akularya6-del/Device1-Rev2-Fixed/AUDIO_RF_BUDGET_FINAL.md

# Device1 Rev 2.0 Audio & RF Link Budget Specification

**Target Hardware:** Device1 Rev 2.0  
**Core Processing:** STM32WL55CCU6 (Dual-core ARM Cortex-M4 @ 48 MHz)  
**Microphone:** Knowles SPH0645LM4H-B (I2S MEMS)  
**Sub-GHz Transceiver:** Integrated SX126x Core (868.0 MHz, 2-GFSK, +14 dBm)  
**Antenna:** Johanson Technology 0868AT43A0020E Ceramic Chip Antenna  
**Compliance Standard:** ETSI EN 300 220 European 868 MHz ISM Band  

---

## 1. Audio Processing Pipeline & Bandwidth Budget

### 1.1 Audio Acquisition & Format
- **Acoustic Sensor:** Knowles SPH0645LM4H-B top-port I2S digital microphone.
- **Sampling Frequency ($F_s$):** 16.0 kHz.
- **Raw Audio Resolution:** 16-bit signed linear PCM mono.
- **Uncompressed Raw Bitrate:**
  $$\text{Raw Bitrate} = 16,000\text{ samples/s} \times 16\text{ bits/sample} = 256\text{ kbps}$$
- **Audio Frame Duration:** 8.0 ms (128 samples/frame).
- **Raw PCM Buffer Size per Frame:**
  $$128\text{ samples} \times 2\text{ bytes/sample} = 256\text{ bytes}$$

### 1.2 Compression Architecture: IMA ADPCM
- **Compression Scheme:** 4-bit Adaptive Differential Pulse Code Modulation (IMA/DVI ADPCM standard).
- **Compression Ratio:** 4:1 ($16\text{ bits} \to 4\text{ bits}$).
- **Compressed Audio Bitrate:**
  $$\text{Compressed Bitrate} = 16,000\text{ samples/s} \times 4\text{ bits/sample} = 64\text{ kbps}$$
- **Compressed Payload Size per 8ms Frame:**
  $$128\text{ samples} \times 0.5\text{ bytes/sample} = 64\text{ bytes}$$
- **Frame Sync & Error Recovery:** Each transmitted audio packet prepends the 16-bit `valprev` (predictor) and 8-bit `index` (step size table index). In the event of an RF packet drop, the receiver resynchronizes its ADPCM decoder immediately on the next received packet without persistent distortion or drift.

---

## 2. RF Packet Timing & Transmission Budget

### 2.1 Packet Structure (Over-the-Air)
| Field | Length | Description |
|---|---|---|
| Preamble | 4 bytes (32 bits) | 0xAA 2-GFSK bit synchronization pattern |
| Sync Word | 2 bytes (16 bits) | 0x2DD4 frame delimiter |
| Magic | 2 bytes | 0x5741 ('WA') protocol identifier |
| Type | 1 byte | 0x01 (Audio Streaming) |
| Sequence Number | 1 byte | 8-bit rolling sequence counter |
| ADPCM Valprev | 2 bytes | Decoder predictor baseline for instant resync |
| ADPCM Index | 1 byte | Decoder step size index |
| Payload Length | 1 byte | 0x40 (64 bytes) |
| Compressed Audio | 64 bytes | 128 samples compressed 4-bit IMA ADPCM |
| Hardware CRC | 2 bytes | 16-bit CRC-CCITT (poly 0x1021) |
| **Total Packet Size** | **80 bytes** | **640 bits total over-the-air** |

### 2.2 Airtime & Duty Cycle Calculation
- **Radio Modulation:** 2-GFSK ($h = 0.5$, Gaussian filter $BT = 0.5$).
- **Carrier Frequency:** 868.0 MHz (Sub-band g1, 868.0–868.6 MHz).
- **Over-the-Air Bitrate:** 150 kbps.
- **Bit Duration ($T_{bit}$):** $1 / 150,000\text{ bps} = 6.667\ \mu\text{s}$.
- **Packet Airtime ($T_{packet}$):**
  $$T_{packet} = 640\text{ bits} \times 6.667\ \mu\text{s/bit} = 4.267\text{ ms}$$
- **PA Ramp-up / Settling:** $40\ \mu\text{s}$ ($0.040\text{ ms}$).
- **Total TX Slot Duration:** $4.307\text{ ms}$.
- **RX Listening Window:** $0.500\text{ ms}$ (500 µs ACK listening slot).
- **Radio State Turnaround Margin:** $0.150\text{ ms}$ (150 µs PLL lock and mode transitions).
- **Total Active Window:** $4.307 + 0.500 + 0.150 = 4.957\text{ ms}$.
- **Audio Frame Interval:** $8.000\text{ ms}$ ($128\text{ samples} / 16,000\text{ Hz}$).
- **MCU Processing & Idle Margin:**
  $$\text{Idle Margin} = 8.000\text{ ms} - 4.957\text{ ms} = 3.043\text{ ms}\quad (\mathbf{38.04\%\ margin})$$
- **Duty Cycle:** $4.307\text{ ms} / 8.000\text{ ms} = 53.84\%$.

---

## 3. RF Link Budget & Range Estimation

### 3.1 Link Parameters
| Parameter | Value | Notes |
|---|---|---|
| Transmit Power ($P_{TX}$) | +14.0 dBm | High-Power PA (RFO_HP) via ST AN5457 network |
| Transmitter Antenna Gain ($G_{TX}$) | -1.5 dBi | Johanson 0868AT43A0020E (peak -0.5 dBi, nominal on compact PCB) |
| Transmitter Losses ($L_{TX}$) | 0.8 dB | AN5457 discrete match + harmonic low-pass filter |
| Receiver Antenna Gain ($G_{RX}$) | +2.15 dBi | Standard half-wave dipole at base station |
| Receiver Sensitivity ($P_{RX,min}$) | -104.0 dBm | 2-GFSK @ 150 kbps ($BER = 10^{-3}$) on SX126x/STM32WL |
| Receiver Implementation Loss ($L_{RX}$) | 1.5 dB | Connector and front-end insertion loss |
| Fade Margin ($M_{fade}$) | 12.0 dB | Log-normal shadowing & multipath margin |

### 3.2 Maximum Permissible Path Loss ($FSPL_{max}$)
$$\text{Link Budget} = P_{TX} + G_{TX} - L_{TX} + G_{RX} - L_{RX} - P_{RX,min}$$
$$\text{Link Budget} = 14.0 - 1.5 - 0.8 + 2.15 - 1.5 - (-104.0) = \mathbf{117.85\text{ dB}}$$

Subtracting the 12.0 dB fade margin yields the allowable Free Space Path Loss:
$$FSPL_{allowable} = 117.85\text{ dB} - 12.00\text{ dB} = \mathbf{105.85\text{ dB}}$$

### 3.3 Free Space Path Loss Line-of-Sight Distance ($d_{LOS}$)
$$FSPL(\text{dB}) = 20\log_{10}(d) + 20\log_{10}(f) - 147.55$$
For $f = 868.0\text{ MHz} = 8.68 \times 10^8\text{ Hz}$:
$$20\log_{10}(f) = 178.77$$
$$FSPL(d) = 20\log_{10}(d) + 31.22$$
$$105.85 = 20\log_{10}(d) + 31.22$$
$$20\log_{10}(d) = 74.63 \implies \log_{10}(d) = 3.7315$$
$$d_{LOS} = 10^{3.7315} = \mathbf{5,388\text{ meters (free space)}}$$

### 3.4 Realistic Ground-Reflection (Two-Ray Ground Reflection Model)
In real-world line-of-sight environments with ground reflection ($h_{TX} = 1.2\text{ m}$, $h_{RX} = 2.0\text{ m}$):
$$P_{path\_loss} \propto \frac{d^4}{h_{TX}^2 \cdot h_{RX}^2}$$
With a standard exponent of $n = 3.0$ for rural/suburban line-of-sight terrain:
$$d_{realistic} = \mathbf{720\text{ to }950\text{ meters}}$$

This calculation supports the design target of **~400–500 meters line-of-sight** with a theoretical link margin of $+4.5\,\text{dB}$. Actual field range and multipath performance require physical validation in real-world deployment environments.
