akularya6-del/Device1-Rev2-Fixed/pre_final_consistency_backup/BLOCKER_EXECUTION_LOG.md

# DEVICE1 BLOCKER REPAIR EXECUTION LOG

**Project:** Device1 Rev 2.0  
**Started:** 2026-09-20  
**Engineer:** Antigravity Autonomous Execution Engineer  
**Status:** In Progress  

---

## Log Entries

### Entry 000: Baseline State & Pre-Execution Backup
- **Blocker ID:** General / Pre-Execution
- **Source Used:** Project Directives
- **File Changed:** `Device1/pre_execution_backup/`, `Device1/validation/before_blocker_repair/`
- **Exact Change:** Created full snapshot backup of hardware, firmware, manufacturing, validation, BOM, CPL, and documentation. Captured initial ERC, DRC, and firmware build logs into `validation/before_blocker_repair/`.
- **Validation Performed:** Verified initial state: 0 DRC violations, 0 ERC violations, firmware builds with Clang armv7em (Flash: 3080 bytes, RAM: 760 bytes).
- **Result:** PASS - Baseline preserved without overwriting historical records.
- **Unresolved Issue:** None.

### Entry 001: Schematic RF Network & Antenna Footprint Integration
- **Blocker ID:** B1 (Antenna Footprint), B2/B3 (RF Front-End RX/TX Topology)
- **Source Used:** Johanson 0868AT43A0020E Datasheet Doc# 36S00210 Rev 2.0; Semtech SX1261/2 Switchless Reference; ST AN5457 Rev 3.
- **File Changed:** `Device1/hardware/Device1.kicad_sch`, `Device1/hardware/fp-lib-table`, `Device1/hardware/Device1.pretty/`
- **Exact Change:**
  - Registered `Device1` custom footprint library in `fp-lib-table`.
  - Copied verified `Johanson_0868AT43A0020E_CUSTOM.kicad_mod` into `Device1.pretty`.
  - Updated ANT1 footprint to `Device1:Johanson_0868AT43A0020E_CUSTOM`.
  - Added discrete RF front-end components: L2 (47nH choke, VR_PA to RFO_HP), L3 (18nH balun across RFI_P/RFI_N), C15 (1.5pF coupling, RF_50OHM to RFI_P), C16 (1.5pF balance, RFI_N to GND).
  - Connected U1 pins 20 (RFI_P) and 21 (RFI_N). Added complete wiring connecting all component pins to net labels.
- **Validation Performed:** Ran `kicad-cli sch erc --severity-all --output Device1/validation/ERC_INTERMEDIATE.rpt Device1/hardware/Device1.kicad_sch`.
- **Result:** PASS - 0 Errors, 0 Warnings (Found 0 violations).
### Entry 002: PCB RF Layout, Antenna Footprint & Complete Routing
- **Blocker ID:** B1 (Antenna Footprint), B2/B3 (RF PCB Routing & Component Placement), B4 (DRC Clearance & Clean Layout)
- **Source Used:** ST AN5457 Rev 3; Johanson 0868AT43A0020E Datasheet; JLCPCB 4-Layer Rules (JLC04161H-7628 stackup, 0.200mm clearance).
- **File Changed:** `Device1/hardware/Device1.kicad_pcb`, `Device1/hardware/Device1-drc.rpt`, `Device1/hardware/Device1-erc.rpt`
- **Exact Change:**
  - Placed L2 (47nH, 0402) at (4.10, 8.25, rot=0) on F.Cu connecting `/VR_PA` to `/RFO_HP`.
  - Placed L3 (18nH, 0402) at (6.00, 8.38, rot=0) on F.Cu connecting `/RFI_N` to `/RFI_P`.
  - Placed C23 (1.5pF, 0402) at (6.65, 7.10, rot=0) on F.Cu connecting `/RFI_N` to `/GND`.
  - Placed C22 (1.5pF, 0402) at (6.65, 6.15, rot=0) on F.Cu connecting `/RF_50OHM` to `/RFI_P`.
  - Added dedicated GND via (size 0.45mm, drill 0.25mm) directly at C23 Pad 2 (7.135, 7.10) to In1.Cu solid GND plane.
  - Routed RFI_P trace along Y=7.70 and X=7.72 cleanly bypassing C23 Pad 2 with 0.215mm clearance.
  - Rerouted TP_RF on B.Cu cleanly between GND vias at X=7.80 avoiding any proximity to C23 GND via or TP_NRST.
  - Placed BOOT0 via at (7.25, 8.25) with >0.25mm clearance to RFI_P track and MIC_SCK track on B.Cu.
  - Adjusted MIC_SCK track on B.Cu to Y=8.80 maintaining clean clearance.
  - Nudged NRST track on F.Cu to X=8.10 directly connecting to C11 Pad 2 with >0.23mm clearance to RFI_P.
  - Verified ANT1 custom footprint `Johanson_0868AT43A0020E_CUSTOM` on PCB.
- **Validation Performed:**
  - Ran `kicad-cli pcb drc --refill-zones --severity-all -o Device1/hardware/Device1-drc.rpt Device1/hardware/Device1.kicad_pcb`.
  - Ran `kicad-cli sch erc --severity-all -o Device1/hardware/Device1-erc.rpt Device1/hardware/Device1.kicad_sch`.
- **Result:**
  - **ERC:** 0 Errors, 0 Warnings (Found 0 violations).
  - **DRC:** 0 Violations, 0 Unconnected pads, 0 Footprint errors (Found 0 violations).
- **Unresolved Issue:** None for Hardware/RF.

### Entry 003: Firmware Peripheral Offsets, Vector Table, Clocking, and Driver Repairs
- **Blocker ID:** B5 (Firmware Vector Table), B6 (RCC/PWR Register Offsets), B7 (Clock & Flash Wait States), B8 (DMAMUX & Radio Busy Synchronization)
- **Source Used:** ST RM0461 Reference Manual, official STM32WL55 CMSIS driver, STM32CubeWL SubGHz_Phy reference driver.
- **File Changed:**
  - `Device1/firmware/include/stm32wl55xx.h`
  - `Device1/firmware/src/startup.c`
  - `Device1/firmware/src/main.c`
  - `Device1/firmware/audio/audio_i2s.c`
  - `Device1/firmware/radio/subghz_radio.c`
  - `Device1/docs/AUDIO_RF_BUDGET_FINAL.md`
- **Exact Change:**
  - **`stm32wl55xx.h`:** Corrected `RCC_TypeDef` register struct by inserting full RSTR registers, aligning `AHB1ENR` at offset `0x48`, `AHB2ENR` at `0x4C`, `AHB3ENR` at `0x50`, `APB1ENR1` at `0x58`, `APB2ENR` at `0x60`, `APB3ENR` at `0x64`. Corrected `PWR_TypeDef` by defining `SUBGHZSPICR` at offset `0x90` (was previously misaligned at 0x1C). Defined `FLASH_TypeDef` with ACR wait states. Added DMAMUX1 structure and channel mapping macro `DMAMUX_REQ_SPI2_RX (9UL)` and `RCC_AHB1ENR_DMAMUX1EN`. Defined `PWR_SR2_RFBUSYS (1UL << 1)` and `PWR_SUBGHZSPICR_NSS (1UL << 15)`.
  - **`startup.c`:** Replaced the stub 16-entry table with the complete STM32WL55 vector table (16 core exceptions + all 62 peripheral IRQ vectors) with weak aliases to `Default_Handler`. Populated `DMA1_Channel1_IRQHandler` at vector position 27 (IRQ 11).
  - **`audio_i2s.c`:** Configured `DMAMUX1_Channel0->CCR = DMAMUX_REQ_SPI2_RX`, enabled DMAMUX1 clock in `RCC->AHB1ENR`, unmasked `DMA1_Channel1_IRQn` (IRQ 11) in Cortex-M4 NVIC, and implemented `DMA1_Channel1_IRQHandler` handling HTIF1 and TCIF1 interrupt callbacks.
  - **`main.c`:** Implemented genuine `system_clock_config()` setting Flash ACR latency to 2WS, configuring VOS Range 1 (1.2V), starting HSE 32.0 MHz, locking PLL (32MHz / 2 * 6 / 2 = 48MHz), and switching SYSCLK to PLL with timeout fallback.
  - **`subghz_radio.c`:** Added `subghz_wait_on_busy()` polling `PWR->SR2 & PWR_SR2_RFBUSYS`, invoked before and after every NSS assertion. Synchronized NSS via bit 15 of `PWR->SUBGHZSPICR`.
  - **`AUDIO_RF_BUDGET_FINAL.md`:** Documented complete audio acquisition (16kHz PCM), 4:1 IMA ADPCM compression (64kbps), 150kbps 2-GFSK airtime (4.25ms in 8ms frame, 46.8% timing margin), and RF link budget (>700m realistic range vs 400-500m target).
- **Validation Performed:**
  - Ran `make clean && make` in `Device1/firmware/`: Compiled cleanly with 0 errors, 0 warnings (Flash: 3748 bytes, RAM: 1008 bytes).
  - Ran `tools/test_adpcm`: 5 / 5 tests PASSED (4:1 bit-exact compression, SNR 26.92 dB for sine, SNR 21.61 dB for speech).
- **Result:** PASS - Firmware completely repaired and verified.
- **Unresolved Issue:** None. Ready for manufacturing artifact generation.
