akularya6-del/Device1-Rev2-Fixed/pre_final_consistency_backup/hardware/test_step7_solved_drc.txt

** Drc report for test_step7_solved.kicad_pcb **
** Created on 2026-09-20T17:00:53 **
** Report includes: Errors, Warnings, Exclusions **

** Found 24 DRC violations **
[clearance]: Clearance violation ( clearance 0.2000 mm; actual 0.1000 mm)
    Local override; error
    @(6.6000 mm, 26.2000 mm): Via [/MIC_WS] on F.Cu - B.Cu
    @(1.8630 mm, 25.8000 mm): Track [/GATE_OC] on F.Cu, length 5.6370 mm
[shorting_items]: Items shorting two nets (nets /MIC_WS and /MIC_SD)
    Local override; error
    @(6.6000 mm, 26.2000 mm): Via [/MIC_WS] on F.Cu - B.Cu
    @(0.7500 mm, 26.0000 mm): Track [/MIC_SD] on B.Cu, length 6.7500 mm
[clearance]: Clearance violation ( clearance 0.2000 mm; actual 0.1500 mm)
    Local override; error
    @(0.4500 mm, 13.3000 mm): Track [/MIC_WS] on B.Cu, length 12.9000 mm
    @(3.2000 mm, 15.0000 mm): Track [/MIC_SD] on B.Cu, length 2.4500 mm
[clearance]: Clearance violation ( clearance 0.2000 mm; actual 0.0500 mm)
    Local override; error
    @(0.4500 mm, 26.2000 mm): Track [/MIC_WS] on B.Cu, length 6.1500 mm
    @(0.7500 mm, 26.0000 mm): Track [/MIC_SD] on B.Cu, length 6.7500 mm
[clearance]: Clearance violation ( clearance 0.2000 mm; actual 0.1750 mm)
    Local override; error
    @(2.2000 mm, 15.7500 mm): Pad 1 [/SWDIO] of TP_SWDIO on B.Cu
    @(3.2000 mm, 15.0000 mm): Track [/MIC_SD] on B.Cu, length 2.4500 mm
[clearance]: Clearance violation ( clearance 0.2000 mm; actual 0.0500 mm)
    Local override; error
    @(12.1500 mm, 12.0000 mm): Track [/LED_R_DRV] on B.Cu, length 6.0000 mm
    @(11.8000 mm, 12.7500 mm): Via [/CHG_STAT] on F.Cu - B.Cu
[clearance]: Clearance violation ( clearance 0.2000 mm; actual 0.1000 mm)
    Local override; error
    @(7.5000 mm, 25.8000 mm): Track [/GATE_OC] on F.Cu, length 1.6000 mm
    @(7.5000 mm, 26.2000 mm): Via [/MIC_SD] on F.Cu - B.Cu
[tracks_crossing]: Tracks crossing
    Local override; error
    @(11.8000 mm, 17.8000 mm): Track [/CHG_STAT] on B.Cu, length 1.9698 mm
    @(11.4000 mm, 16.5000 mm): Track [/LED_B_DRV] on B.Cu, length 1.5000 mm
[shorting_items]: Items shorting two nets (nets /CHG_STAT and /LED_B_DRV)
    Local override; error
    @(11.8000 mm, 17.8000 mm): Track [/CHG_STAT] on B.Cu, length 1.9698 mm
    @(11.4000 mm, 18.0000 mm): Track [/LED_B_DRV] on B.Cu, length 10.0000 mm
[clearance]: Clearance violation ( clearance 0.2000 mm; actual 0.1000 mm)
    Local override; error
    @(11.8000 mm, 12.7500 mm): Via [/CHG_STAT] on F.Cu - B.Cu
    @(11.4000 mm, 8.8000 mm): Track [/LED_B_DRV] on B.Cu, length 7.7000 mm
[clearance]: Clearance violation ( clearance 0.2000 mm; actual 0.1000 mm)
    Local override; error
    @(1.8630 mm, 25.8000 mm): Track [/GATE_OC] on F.Cu, length 5.6370 mm
    @(7.5000 mm, 26.2000 mm): Via [/MIC_SD] on F.Cu - B.Cu
[shorting_items]: Items shorting two nets (nets /MIC_SCK and /3V3)
    Local override; error
    @(8.4000 mm, 27.2000 mm): Via [/MIC_SCK] on F.Cu - B.Cu
    @(8.4000 mm, 27.1360 mm): Track [/3V3] on F.Cu, length 0.9630 mm
[clearance]: Clearance violation ( clearance 0.2000 mm; actual 0.1750 mm)
    Local override; error
    @(12.7200 mm, 10.7500 mm): Track [/3V3] on F.Cu, length 1.7825 mm
    @(12.2000 mm, 10.2500 mm): Via [/LED_R_DRV] on F.Cu - B.Cu
[shorting_items]: Items shorting two nets (nets /3V3 and /MIC_SCK)
    Local override; error
    @(8.5000 mm, 17.4000 mm): Via [/3V3] on F.Cu - B.Cu
    @(9.2000 mm, 16.5000 mm): Track [/MIC_SCK] on In2.Cu, length 1.4142 mm
[shorting_items]: Items shorting two nets (nets /MIC_SCK and /NRST)
    Local override; error
    @(8.2500 mm, 8.8000 mm): Via [/MIC_SCK] on F.Cu - B.Cu
    @(7.7500 mm, 8.6000 mm): Track [/NRST] on F.Cu, length 0.7500 mm
[shorting_items]: Items shorting two nets (nets /MIC_SCK and /3V3)
    Local override; error
    @(8.4000 mm, 27.2000 mm): Via [/MIC_SCK] on F.Cu - B.Cu
    @(8.4000 mm, 27.1360 mm): Pad 5 [/3V3] of MK1 on F.Cu
[clearance]: Clearance violation ( clearance 0.2000 mm; actual 0.1950 mm)
    Local override; error
    @(12.7200 mm, 9.5000 mm): Track [/3V3] on F.Cu, length 1.2500 mm
    @(12.2000 mm, 10.2500 mm): Via [/LED_R_DRV] on F.Cu - B.Cu
[clearance]: Clearance violation ( clearance 0.2000 mm; actual 0.0162 mm)
    Local override; error
    @(8.2000 mm, 17.5000 mm): Track [/MIC_SCK] on In2.Cu, length 9.0000 mm
    @(8.5000 mm, 17.4000 mm): Via [/3V3] on F.Cu - B.Cu
[shorting_items]: Items shorting two nets (nets /MIC_SCK and /3V3)
    Local override; error
    @(8.4000 mm, 27.2000 mm): Track [/MIC_SCK] on F.Cu, length 0.7580 mm
    @(8.4000 mm, 27.1360 mm): Track [/3V3] on F.Cu, length 0.9630 mm
[clearance]: Clearance violation ( clearance 0.2000 mm; actual 0.0500 mm)
    Local override; error
    @(7.7500 mm, 8.6000 mm): Track [/NRST] on F.Cu, length 0.7500 mm
    @(8.2500 mm, 9.5620 mm): Track [/MIC_SCK] on F.Cu, length 0.7620 mm
[clearance]: Clearance violation ( clearance 0.2000 mm; actual 0.1500 mm)
    Local override; error
    @(0.7500 mm, 15.0000 mm): Track [/MIC_SD] on B.Cu, length 11.0000 mm
    @(1.2000 mm, 24.2000 mm): Via [/GND] on F.Cu - B.Cu
[hole_clearance]: Hole clearance violation (board setup constraints hole clearance 0.2000 mm; actual 0.0000 mm)
    Rule: board setup constraints hole; error
    @(8.4000 mm, 27.1360 mm): Pad 5 [/3V3] of MK1 on F.Cu
    @(8.4000 mm, 27.2000 mm): Via [/MIC_SCK] on F.Cu - B.Cu
[solder_mask_bridge]: Front solder mask aperture bridges items with different nets
    Rule: board setup solder mask min width; error
    @(8.4000 mm, 27.2000 mm): Track [/MIC_SCK] on F.Cu, length 0.7580 mm
    @(8.4000 mm, 27.1360 mm): Pad 5 [/3V3] of MK1 on F.Cu
[solder_mask_bridge]: Front solder mask aperture bridges items with different nets
    Rule: board setup solder mask min width; error
    @(8.4000 mm, 27.2000 mm): Via [/MIC_SCK] on F.Cu - B.Cu
    @(8.4000 mm, 27.1360 mm): Pad 5 [/3V3] of MK1 on F.Cu

** Found 1 unconnected pads **
[unconnected_items]: Missing connection between items
    Local override; error
    @(6.7500 mm, 16.4375 mm): Track [/3V3] on F.Cu, length 0.9625 mm
    @(8.2500 mm, 16.4375 mm): Track [/3V3] on F.Cu, length 0.4125 mm

** Found 0 Footprint errors **

** Ignored checks **
    - Footprint has no courtyard defined
    - Track endpoint not centered on via
    - Tuning profile track geometries
    - Footprint doesn't match symbol's footprint filters
    - Footprint component type doesn't match footprint pads

** End of Report **
