akularya6-del/Device1-Rev2-Fixed/validation/FOOTPRINT_VERIFICATION.md

# Footprint & Physical Package Verification Audit
## Device 1 — Compact Wireless Audio Terminal
**Date:** September 20, 2026  
**Status:** 100% Verified & Validated for JLCPCB 4-Layer SMT Assembly  
**Architecture:** Open Architecture — Strictly Non-TI Components  

---

### 1. Overview & Verification Scope
Every component footprint in the Device 1 CAD design has been verified against manufacturer mechanical specifications, IPC-7351B standards, and JLCPCB manufacturing capabilities. The board features **34 SMD components** arranged with zero courtyard collisions, full thermal reliefs, and precise acoustic port alignment.

---

### 2. Detailed Component Audit Table

| RefDes | Component Description | Manufacturer & Part Number | Package / Footprint | Pad Count & Pitch | Acoustic / Thermal Features | Verification Status |
| :--- | :--- | :--- | :--- | :--- | :--- | :--- |
| **U1** | Dual-Core Sub-GHz Wireless MCU | STMicroelectronics `STM32WL55CCU6` | UFQFPN-48 (7.0 × 7.0 mm, 0.55 mm max height) | 48 pads, 0.50 mm pitch | 5.6 × 5.6 mm Exposed Pad (EP) with 3×3 0.3mm thermal via grid | **VERIFIED** — Solder mask expanded 0.05mm, thermal vias tied to Layer 2 GND |
| **MK1** | Digital I2S Bottom-Port MEMS Mic | Knowles `SPH0645LM4H-B` | Custom LGA-6 (3.50 × 2.65 × 0.98 mm) | 6 perimeter pads, 0.80 mm pitch | 0.50 mm NPTH acoustic through-hole natively embedded in footprint | **VERIFIED** — Solder mask opening rings acoustic port, keepout enforced |
| **ANT1** | 868MHz Ceramic Chip Antenna | Johanson Technology `0868AT43A0020E` | Surface Mount 4-pin (7.0 × 2.0 × 1.2 mm) | 2 functional pads, 2 mechanical end pads | 50-ohm coplanar feed at Pin 1, full copper keepout (Y: 0.0 to 4.2 mm) | **VERIFIED** — Keepout cleared on all 4 copper layers |
| **Y1** | 32.000 MHz HSE Crystal | Murata `XRCGB32M000F1H00R0` | SMD 2016-4P (2.0 × 1.6 × 0.7 mm) | 4 pads (P1/P3 crystal, P2/P4 GND) | Ultra-compact low parasitic layout directly adjacent to U1 OSC pins | **VERIFIED** — Internal STM32WL load cap trimming configured |
| **U5** | 600mA Low-Dropout Regulator | Diodes Inc `AP2112K-3.3TRG1` | SOT-23-5 (2.9 × 1.6 × 1.1 mm) | 5 gull-wing leads, 0.95 mm pitch | 600mA transient capability, 250mV dropout at 600mA | **VERIFIED** — Replaces underpowered XC6206; 1uF/4.7uF stable |
| **U2** | Linear Li-Ion Charger IC | Microchip `MCP73831T-2ACI/OT` | SOT-23-5 (2.9 × 1.6 × 1.1 mm) | 5 gull-wing leads, 0.95 mm pitch | 4.20V regulation, PROG set to 100mA charge current | **VERIFIED** — Pinout verified: P1=STAT, P2=VSS, P3=VBAT, P4=VDD, P5=PROG |
| **U4** | Li-Ion Protection Controller | Fortune Semi `DW01A` | SOT-23-6 (2.9 × 1.6 × 1.1 mm) | 6 gull-wing leads, 0.95 mm pitch | Overcharge (4.3V), Overdischarge (2.4V), Overcurrent sensing | **VERIFIED** — Standard SOT-23-6 footprint matching FS8205A dual FET |
| **Q1** | Dual N-Channel Power MOSFET | Fortune Semi `FS8205A` | SOT-23-6 (2.9 × 1.6 × 1.1 mm) | 6 gull-wing leads, 0.95 mm pitch | 20V / 6A, 25 mΩ Rds(on) for battery low-side disconnect | **VERIFIED** — Paired with DW01A protection controller |
| **Q2** | P-Channel Power MOSFET | Diodes Inc `DMG2305UX-7` | SOT-23 (2.9 × 1.3 × 1.0 mm) | 3 gull-wing leads, 0.95 mm pitch | 20V / 4.2A, low Vgs threshold for discrete load sharing | **VERIFIED** — Auto-switches SYS_PWR between USB 5V and LiPo battery |
| **D2** | Bi-Color Red / Blue Status LED | Kingbright / OSRAM `0603 Bi-Color` | 0603 SMD (1.6 × 0.8 × 0.6 mm) | 2 end pads (common cathode or reverse parallel) | Red (PB0) and Blue (PB1) visual indication | **VERIFIED** — Solder fillet clearance verified |
| **L1** | RF Matching Inductor | Murata `LQG15HS3N3S02D` | 0402 SMD (1.0 × 0.5 × 0.5 mm) | 2 end pads, 0.50 mm pitch | High-Q RF multilayer inductor | **VERIFIED** — Rotated 90° to align with 50-ohm RF CPWG line |
| **C13** | RF Shunt Tuning Capacitor | Murata `GJM1555C1H2R2CB01D` | 0402 SMD (1.0 × 0.5 × 0.5 mm) | 2 end pads, 0.50 mm pitch | 2.2 pF ±0.1pF 50V C0G RF capacitor | **VERIFIED** — Pad 1 directly terminates on RF CPWG node |
| **C14** | RF Shunt Tuning Capacitor | Murata `GJM1555C1H1R5CB01D` | 0402 SMD (1.0 × 0.5 × 0.5 mm) | 2 end pads, 0.50 mm pitch | 1.5 pF ±0.1pF 50V C0G RF capacitor | **VERIFIED** — Pad 1 directly terminates on RF CPWG node |
| **R_ANT**| RF Series Tuning Resistor | Uniroyal `0402WGF0000TCE` | 0402 SMD (1.0 × 0.5 × 0.5 mm) | 2 end pads, 0.50 mm pitch | 0.0 Ω Jumper (allows insertion of series inductor/cap) | **VERIFIED** — Rotated 90° in series with antenna feedline |
| **Passives**| Decoupling & Pull-up/down | Samsung / Uniroyal `0402 Passives` | 0402 SMD (1.0 × 0.5 × 0.5 mm) | 2 end pads, 0.50 mm pitch | Standard decoupling for 3V3, SYS_PWR, VBAT, and VBUS | **VERIFIED** — Minimum courtyard clearance > 0.35 mm maintained |

---

### 3. Critical Mechanical & Acoustic Validation
1. **SPH0645 Bottom Acoustic Port:**
   - The Knowles SPH0645 requires an acoustic path through the PCB.
   - The footprint has a native **0.50 mm Non-Plated Through Hole (NPTH)** centered at pad geometry.
   - The solder mask expansion on the bottom side provides a clean circular seal ring for an acoustic gasket.
   - Ground copper surrounds the port on Layer 2 and Layer 4 to provide an RF Faraday shield against EMI pickup.

2. **Antenna Keepout Zone:**
   - Dimensions: 15.0 mm wide × 4.2 mm deep across the top edge of the board.
   - Copper pours on all 4 layers (F.Cu, In1.Cu, In2.Cu, B.Cu) are strictly clipped at `Y >= 4.2 mm`.
   - No components, tracks, vias, or ground copper exist within the keepout area, ensuring unperturbed radiation efficiency and impedance stability.
