akularya6-del/Device1-Rev2-Fixed/pre_final_consistency_backup/hardware/test_1v_drc.txt

** Drc report for test_led_vbus_winner.kicad_pcb **
** Created on 2026-09-20T17:19:58 **
** Report includes: Errors, Warnings, Exclusions **

** Found 1 DRC violations **
[tracks_crossing]: Tracks crossing
    Local override; error
    @(10.0000 mm, 11.0000 mm): Track [/LED_R_DRV] on B.Cu, length 16.0000 mm
    @(8.5500 mm, 23.2500 mm): Track [/VBUS_5V] on B.Cu, length 2.5120 mm

** Found 3 unconnected pads **
[unconnected_items]: Missing connection between items
    Local override; error
    @(4.0625 mm, 13.7500 mm): Pad 32 [/MIC_WS] of U1 on F.Cu
    @(6.6000 mm, 27.1360 mm): Pad 1 [/MIC_WS] of MK1 on F.Cu
[unconnected_items]: Missing connection between items
    Local override; error
    @(8.2500 mm, 9.5625 mm): Pad 17 [/MIC_SCK] of U1 on F.Cu
    @(8.4000 mm, 27.9580 mm): Pad 4 [/MIC_SCK] of MK1 on F.Cu
[unconnected_items]: Missing connection between items
    Local override; error
    @(4.0625 mm, 14.2500 mm): Pad 33 [/MIC_SD] of U1 on F.Cu
    @(7.5000 mm, 27.1360 mm): Pad 6 [/MIC_SD] of MK1 on F.Cu

** Found 0 Footprint errors **

** Ignored checks **
    - Footprint has no courtyard defined
    - Track endpoint not centered on via
    - Tuning profile track geometries
    - Footprint doesn't match symbol's footprint filters
    - Footprint component type doesn't match footprint pads

** End of Report **
