akularya6-del/Device1-Rev2-Fixed/validation/annotated_layout_crop.png

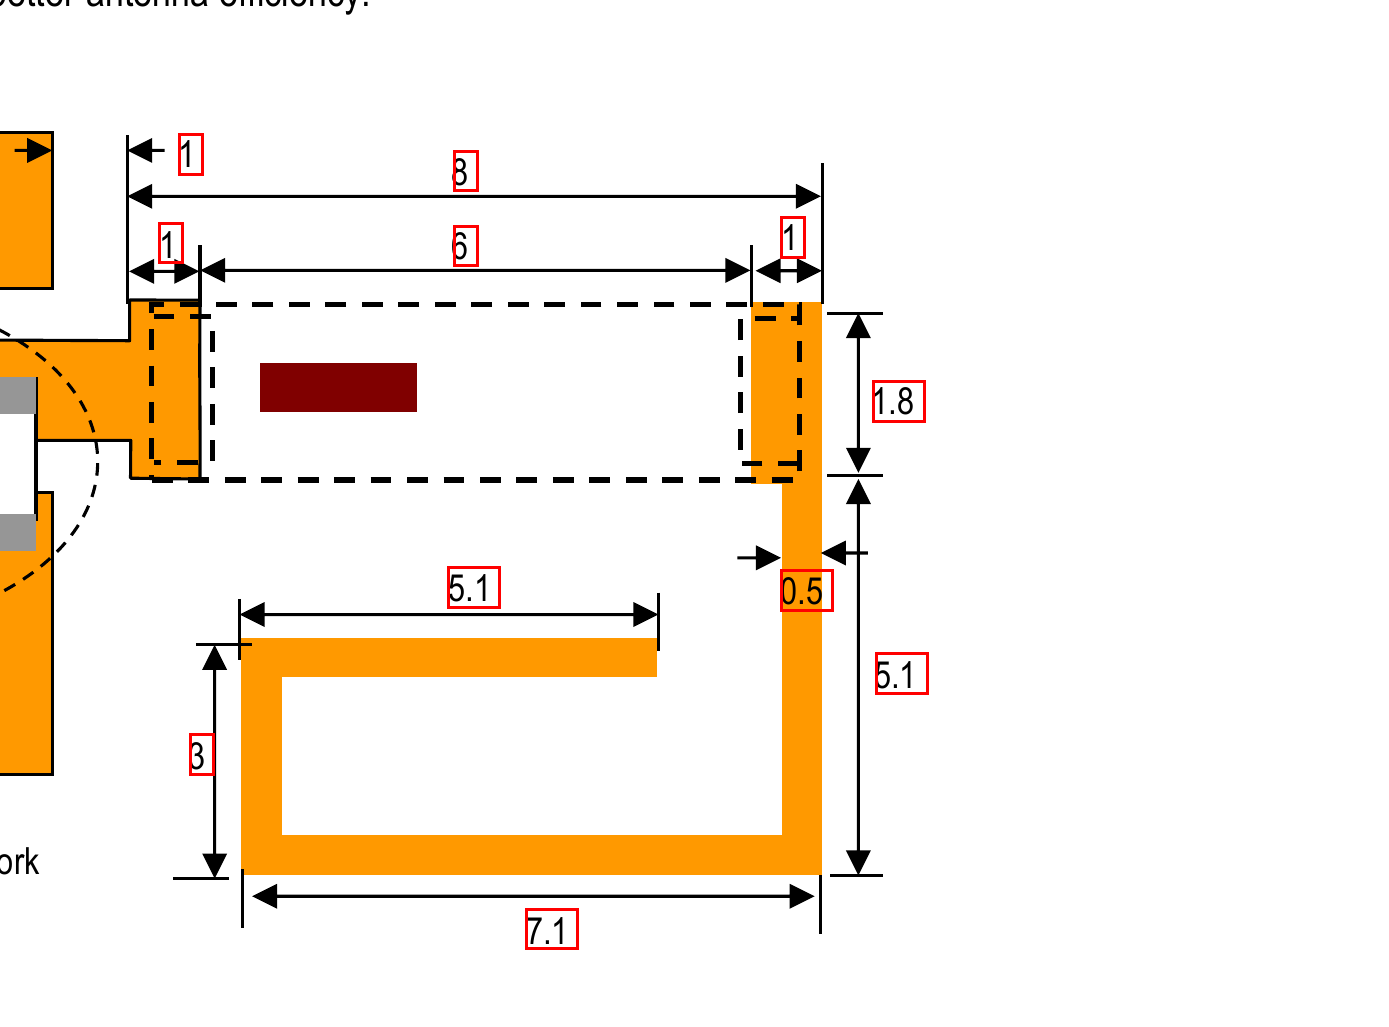
validation/annotated_layout_crop.png
