akularya6-del/Device1-Rev2-Fixed/validation/ant_crop_ds2.png

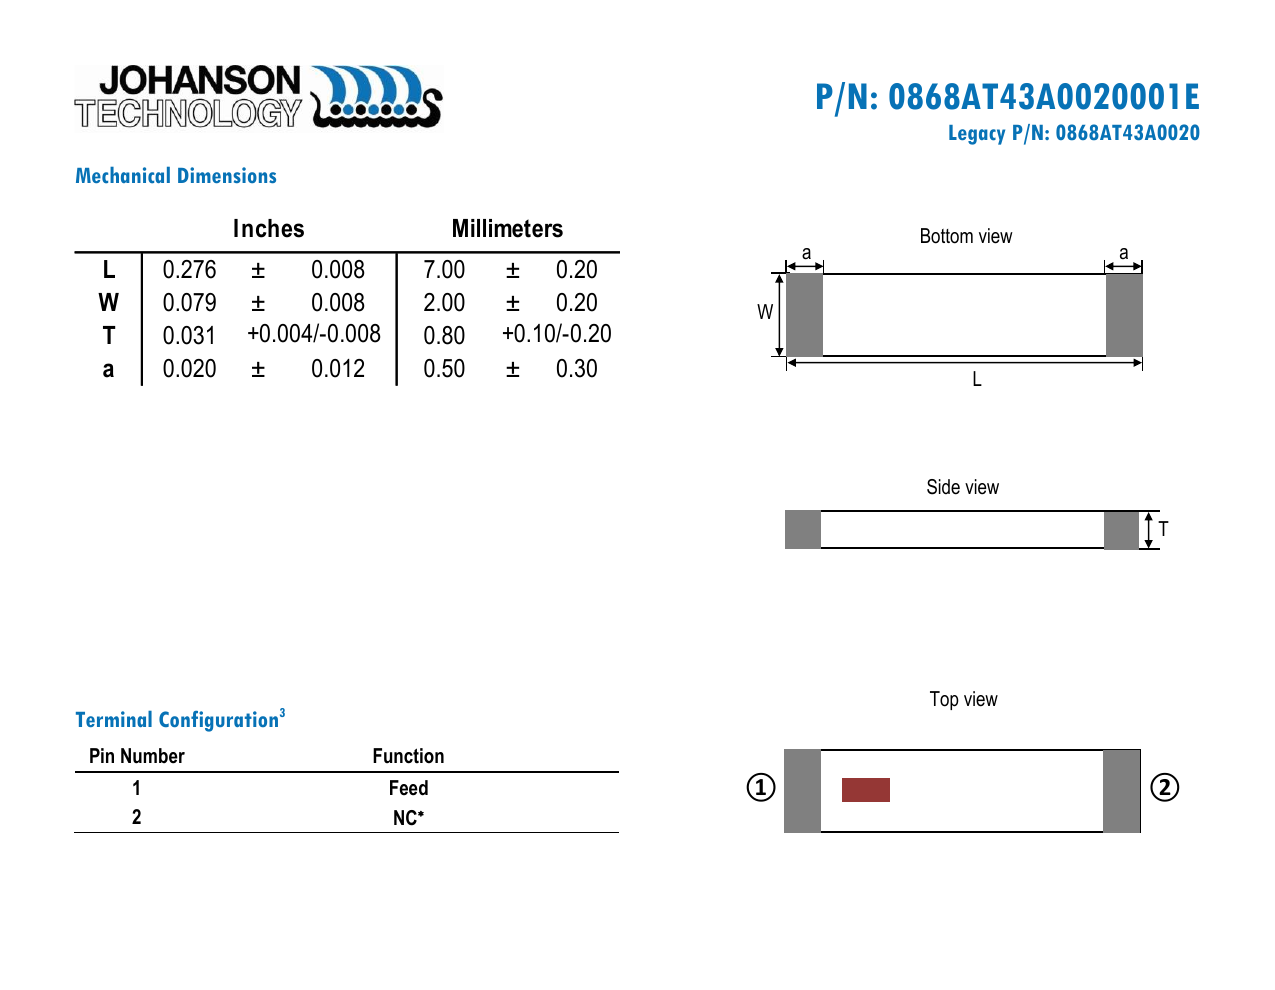
validation/ant_crop_ds2.png
