akularya6-del/Device1-Rev2-Fixed/validation/ant_ds3_300dpi-3.png

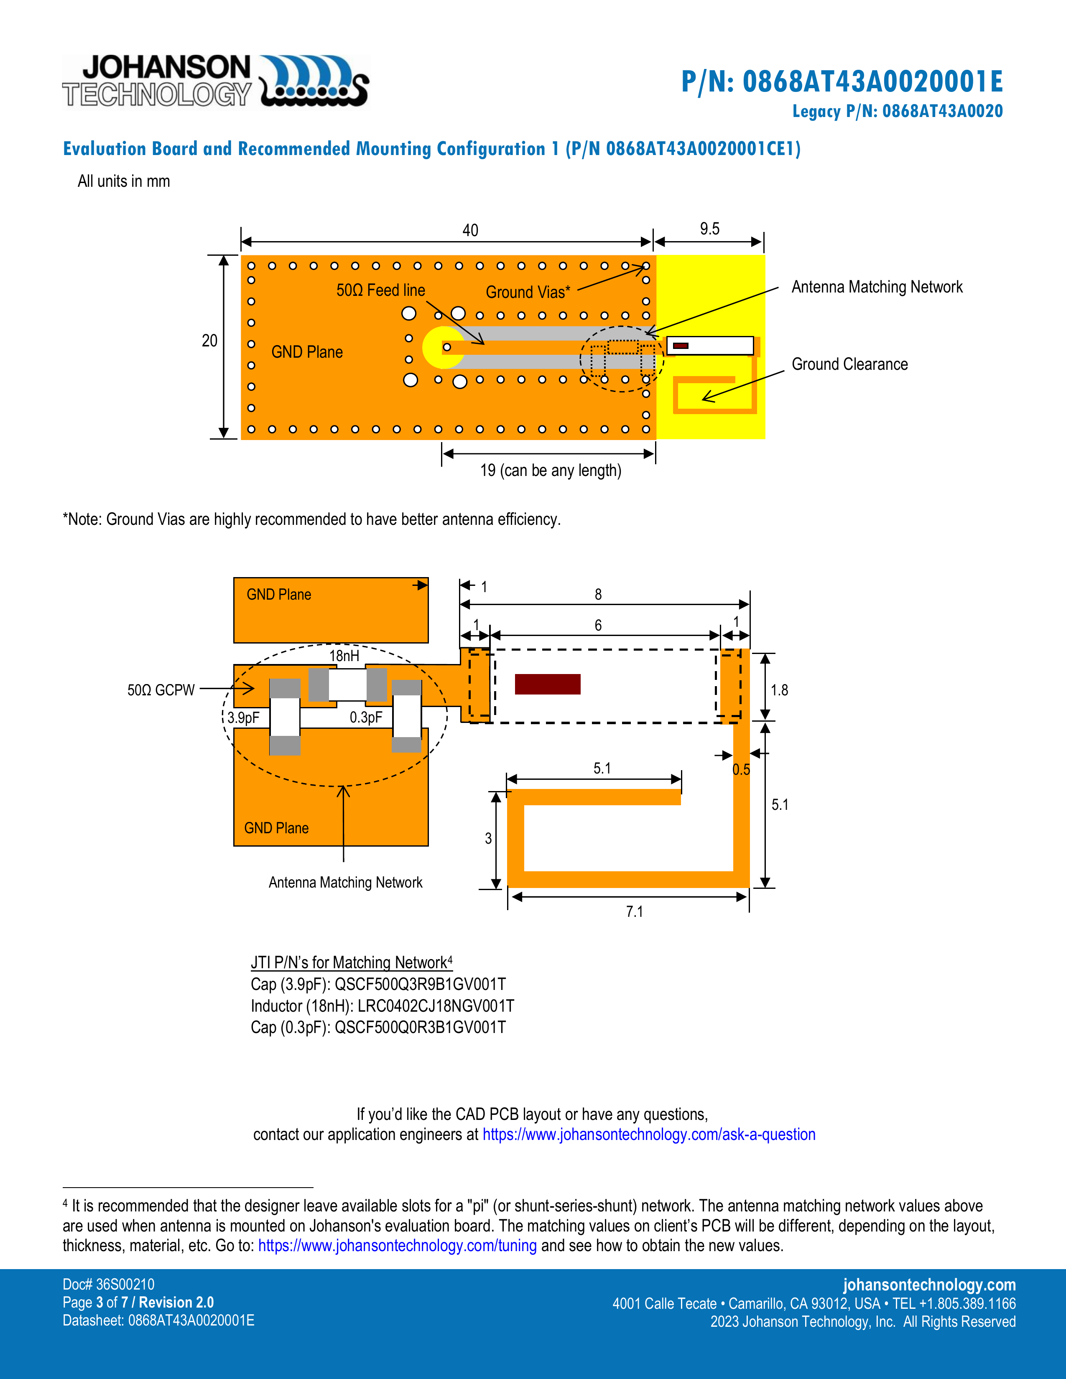
validation/ant_ds3_300dpi-3.png
