akularya6-del/Device1-Rev2-Fixed/validation/ant_ds-2.png

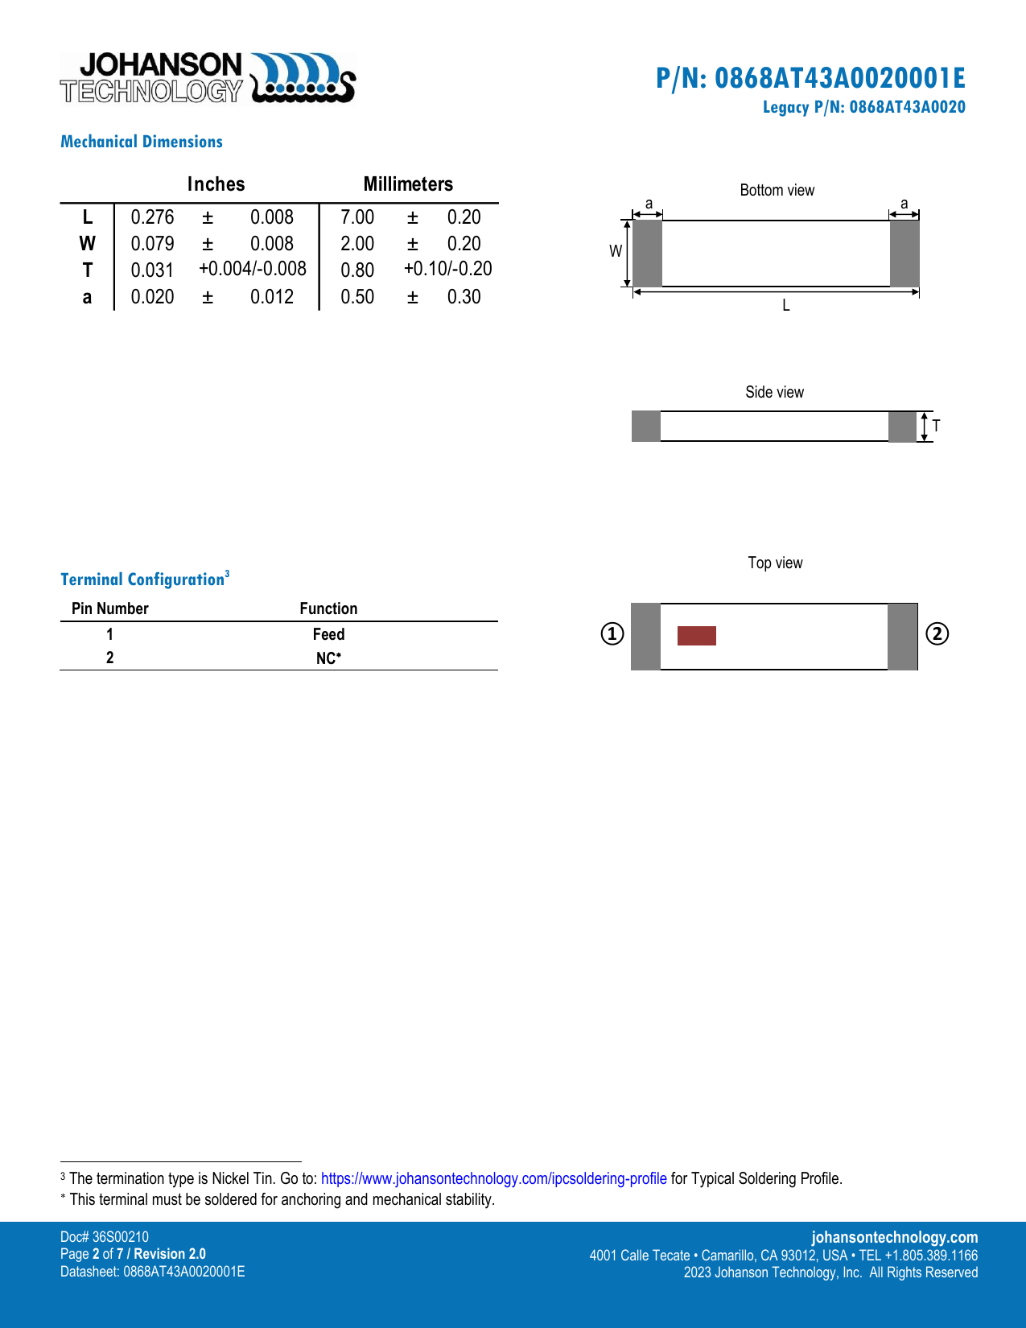
validation/ant_ds-2.png
