akularya6-del/Device1-Rev2-Fixed/validation/ant_only_zoom.png

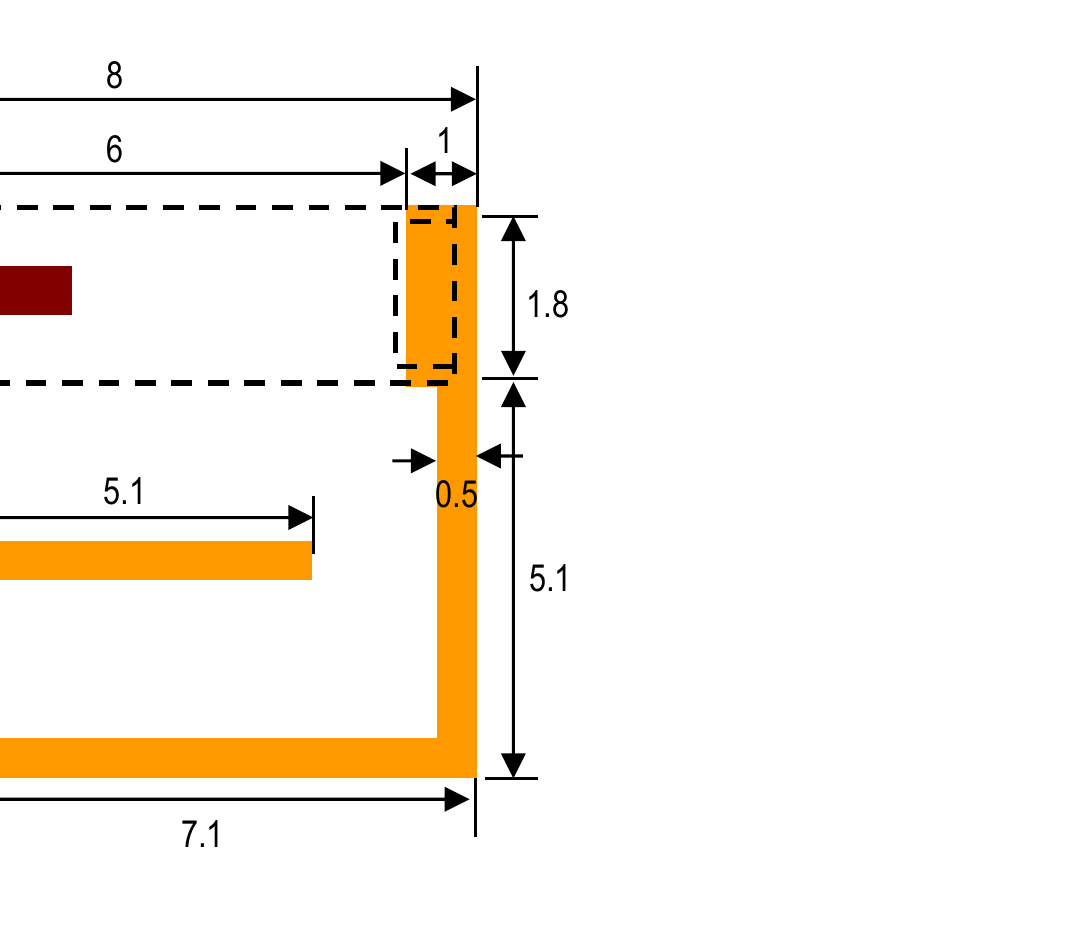
validation/ant_only_zoom.png
