akularya6-del/Device1-Rev2-Fixed/validation/dim_1_1130_1472.png

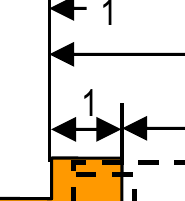
validation/dim_1_1130_1472.png
