akularya6-del/Device1-Rev2-Fixed/validation/dim_1_1150_1383.png

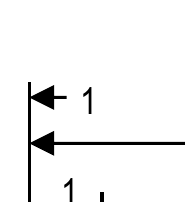
validation/dim_1_1150_1383.png
