akularya6-del/Device1-Rev2-Fixed/validation/dim_1_1752_1466.png

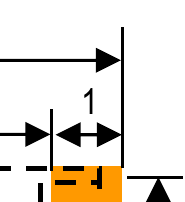
validation/dim_1_1752_1466.png
