akularya6-del/Device1-Rev2-Fixed/validation/dim_3_1161_1983.png

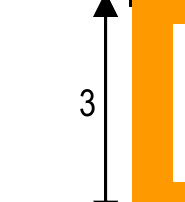
validation/dim_3_1161_1983.png
