akularya6-del/Device1-Rev2-Fixed/validation/dim_5.1_1419_1816.png

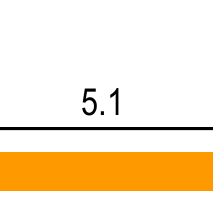
validation/dim_5.1_1419_1816.png
