akularya6-del/Device1-Rev2-Fixed/validation/dim_8_1425_1400.png

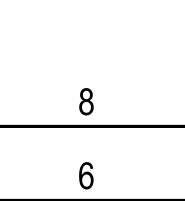
validation/dim_8_1425_1400.png
