akularya6-del/Device1-Rev2-Fixed/pre_final_consistency_backup/firmware/include/string.h

/**
 * @file string.h
 * @brief Minimal freestanding memory manipulation functions for bare-metal ARM
 */

#ifndef EMBEDDED_STRING_H
#define EMBEDDED_STRING_H

#include <stddef.h>

static inline void *memcpy(void *dest, const void *src, size_t n)
{
    unsigned char *d = (unsigned char *)dest;
    const unsigned char *s = (const unsigned char *)src;
    while (n--) {
        *d++ = *s++;
    }
    return dest;
}

static inline void *memset(void *s, int c, size_t n)
{
    unsigned char *p = (unsigned char *)s;
    while (n--) {
        *p++ = (unsigned char)c;
    }
    return s;
}

static inline int memcmp(const void *s1, const void *s2, size_t n)
{
    const unsigned char *p1 = (const unsigned char *)s1;
    const unsigned char *p2 = (const unsigned char *)s2;
    while (n--) {
        if (*p1 != *p2) {
            return *p1 - *p2;
        }
        p1++;
        p2++;
    }
    return 0;
}

#endif /* EMBEDDED_STRING_H */
