akularya6-del/Device1-Rev2-Fixed/pre_final_consistency_backup/hardware/test_intersections.py

import math

# Check 2D segment intersection
def ccw(A, B, C):
    return (C[1]-A[1]) * (B[0]-A[0]) > (B[1]-A[1]) * (C[0]-A[0])

def intersect(A, B, C, D):
    return ccw(A,C,D) != ccw(B,C,D) and ccw(A,B,C) != ccw(A,B,D)

print("Intersection tester ready.")
